icsom/5x4-soundboard/eagle-files/arduino_pro_mini/5x4-soundboard_arduino_pro_mini.png

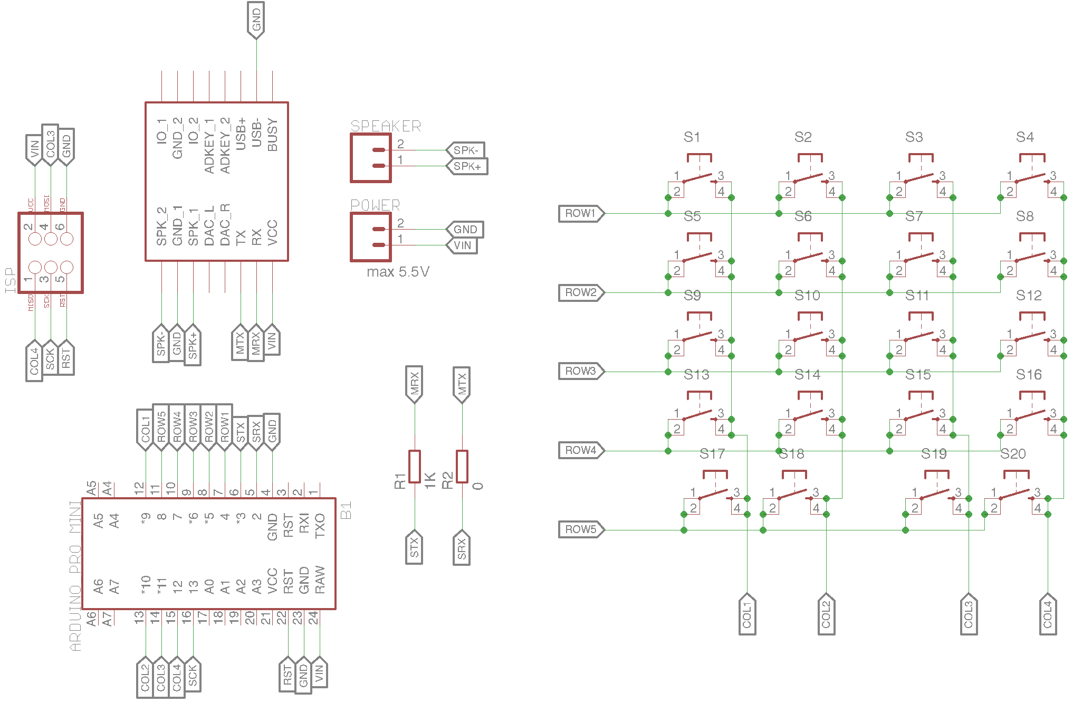
eagle-files/arduino_pro_mini/5x4-soundboard_arduino_pro_mini.png
