icsom/5x4-soundboard/eagle-files/atmega328p_dip/5x4-soundboard_328p_dip.png

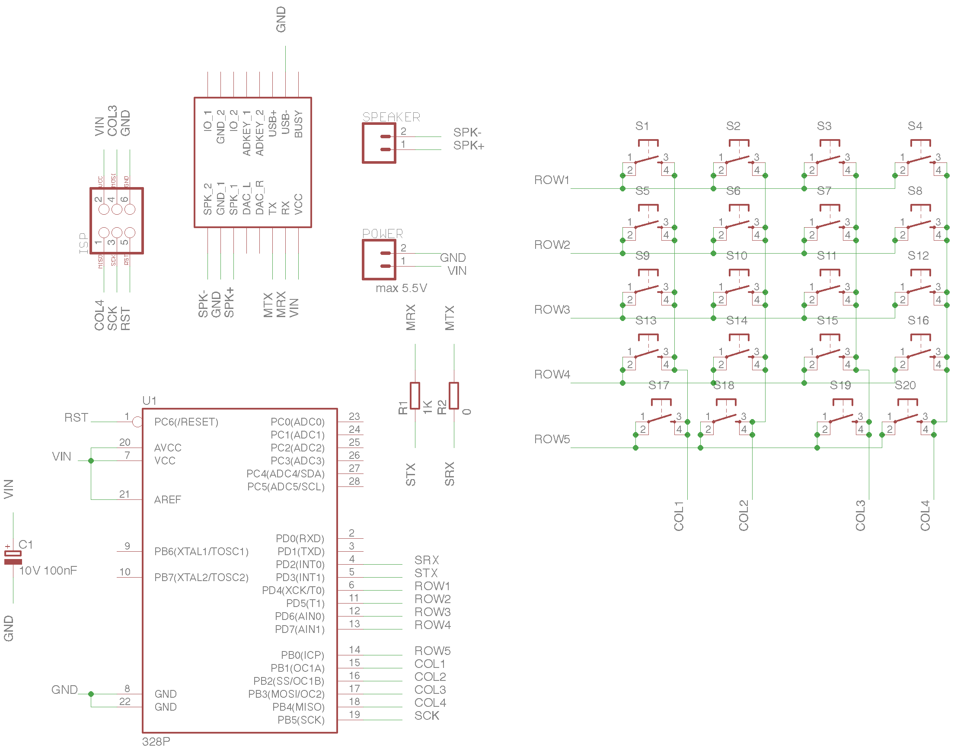
eagle-files/atmega328p_dip/5x4-soundboard_328p_dip.png
