icsom/5x4-soundboard/pictures/arduino_pro_mini/pcb_populated_front.jpg

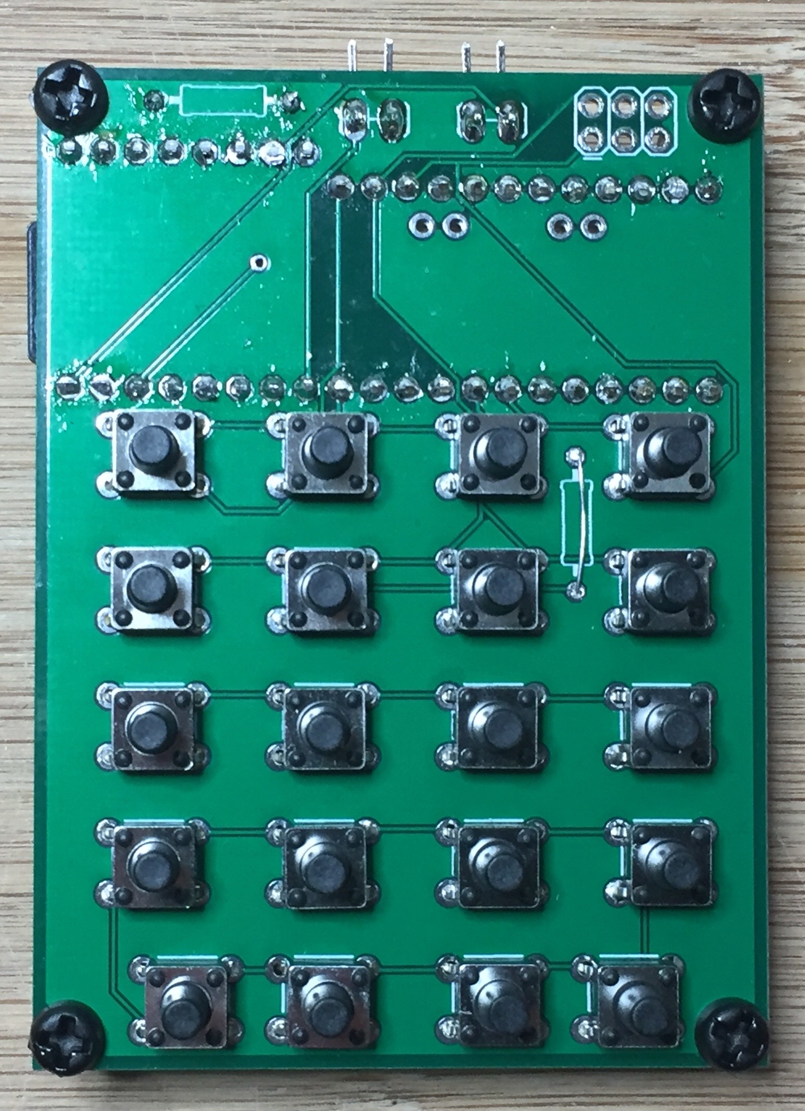
pictures/arduino_pro_mini/pcb_populated_front.jpg
