icsom/5x4-soundboard/pictures/atmega328p_dip/pcb_populated_back.jpg

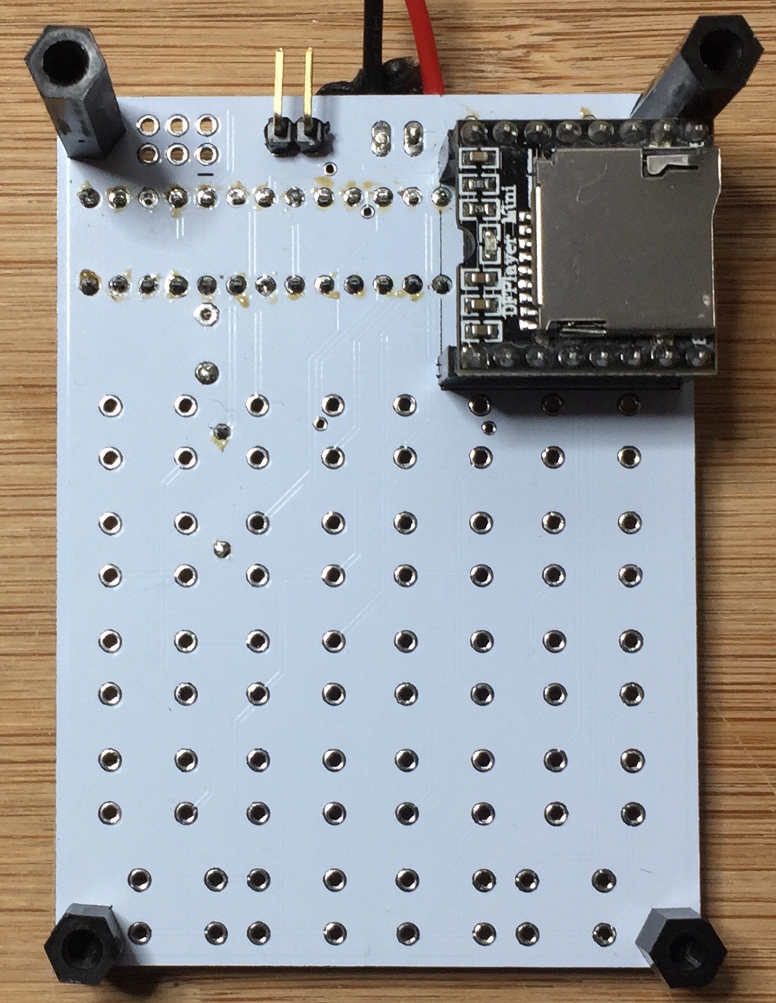
pictures/atmega328p_dip/pcb_populated_back.jpg
