icsom/5x4-soundboard/pictures/atmega328p_tqfp/pcb_populated_front.jpg

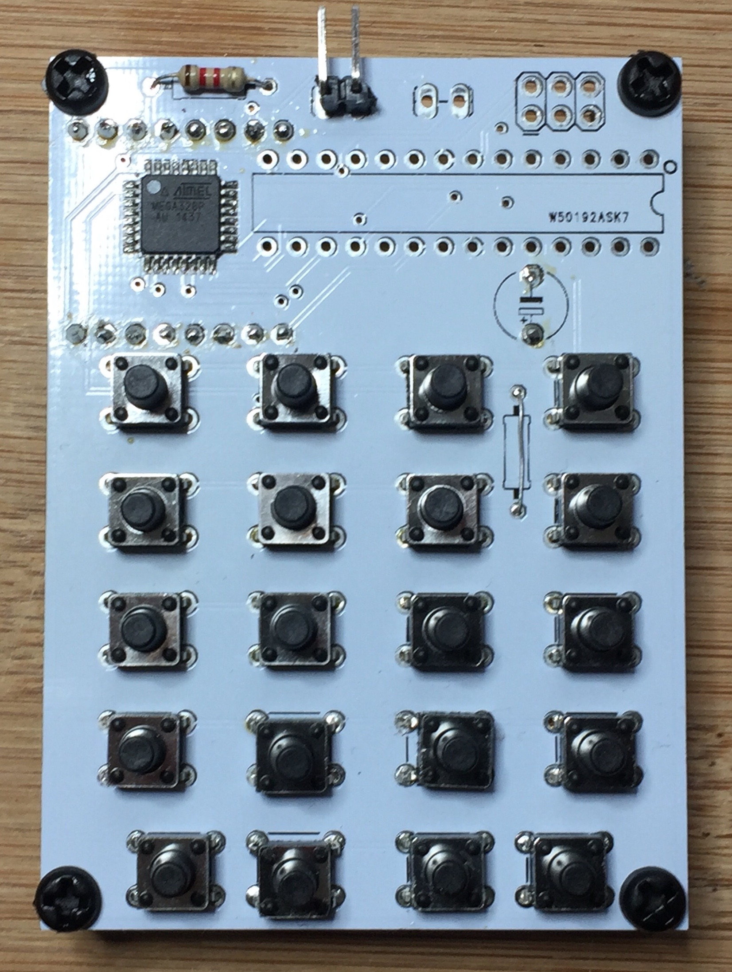
pictures/atmega328p_tqfp/pcb_populated_front.jpg
